JungleGim/PyDash_PCB/design_and_ref_docs/waveshare_display/electrical_specs.png

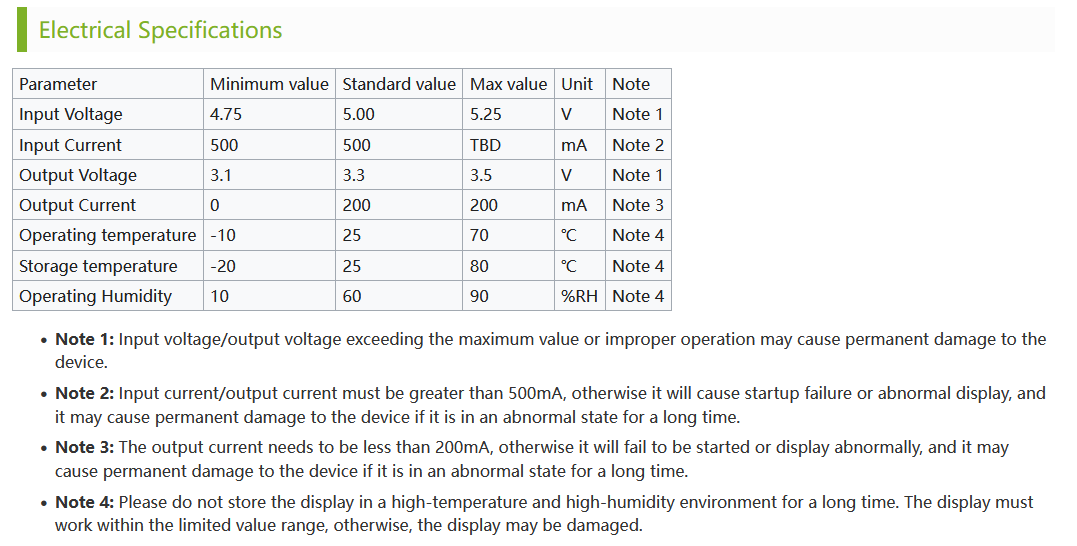
design_and_ref_docs/waveshare_display/electrical_specs.png
