JungleGim/PyDash_PCB/Images/Rev2a_Render.png

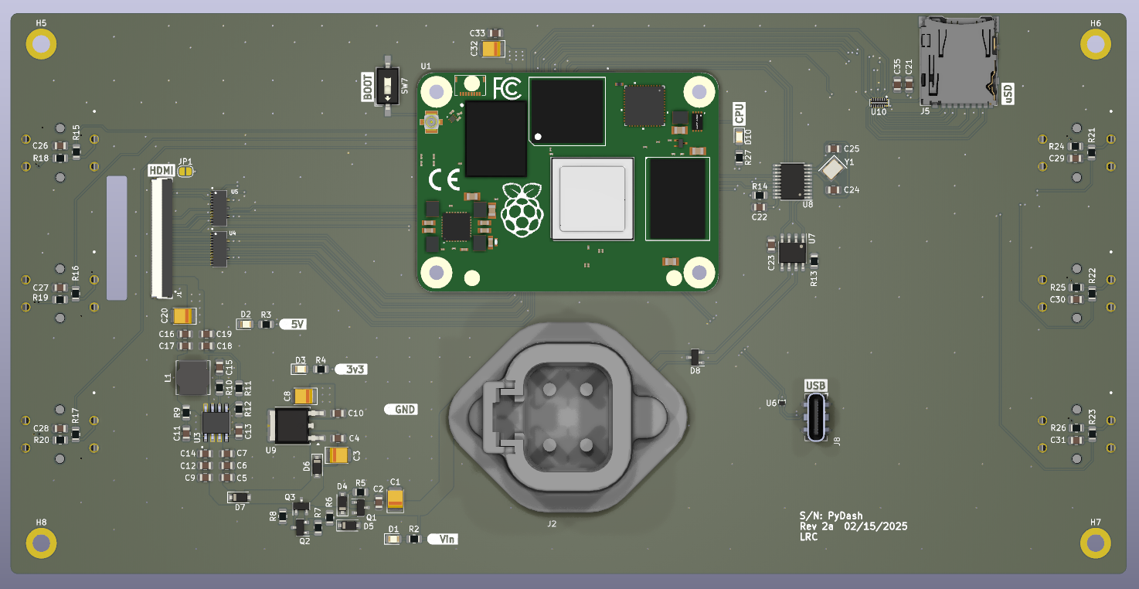
Images/Rev2a_Render.png
