JungleGim/PyDash_PCB/PCB_files/user_lib/CSD23280F3/CSD23280F3.step

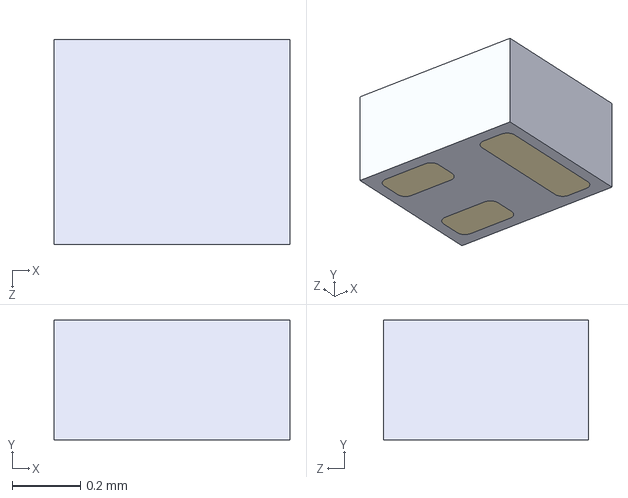
[picture p23: CAD file, 2026-02-16]
PCB_files/user_lib/CSD23280F3/CSD23280F3.step
0.69 x 0.35 x 0.6 mm
