JungleGim/PyDash_PCB/PCB_files/user_lib/B3F_5050/B3F-5050_12mm_keycap_solidworks_assy/B3F-5050.SLDASM

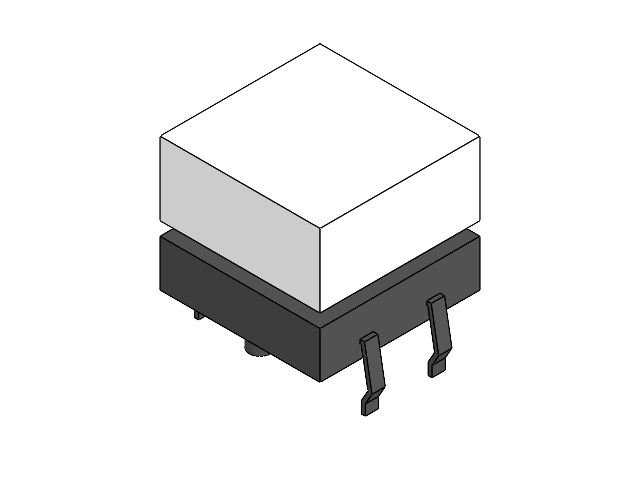
[picture p24: CAD file, 2026-03-10]
PCB_files/user_lib/B3F_5050/B3F-5050_12mm_keycap_solidworks_assy/B3F-5050.SLDASM
B3F_5050_BASE_3
B3F_5050_BUTTON_3
12mm_keycap
